sonic2000gr/RainbowProject/Schematics/IO Decoder/rescue-backup/IODecoder-2018-12-28-10-11-45.sch

## KiCad design Schematics/IO Decoder/rescue-backup/IODecoder-2018-12-28-10-11-45.sch (2017-12-11)

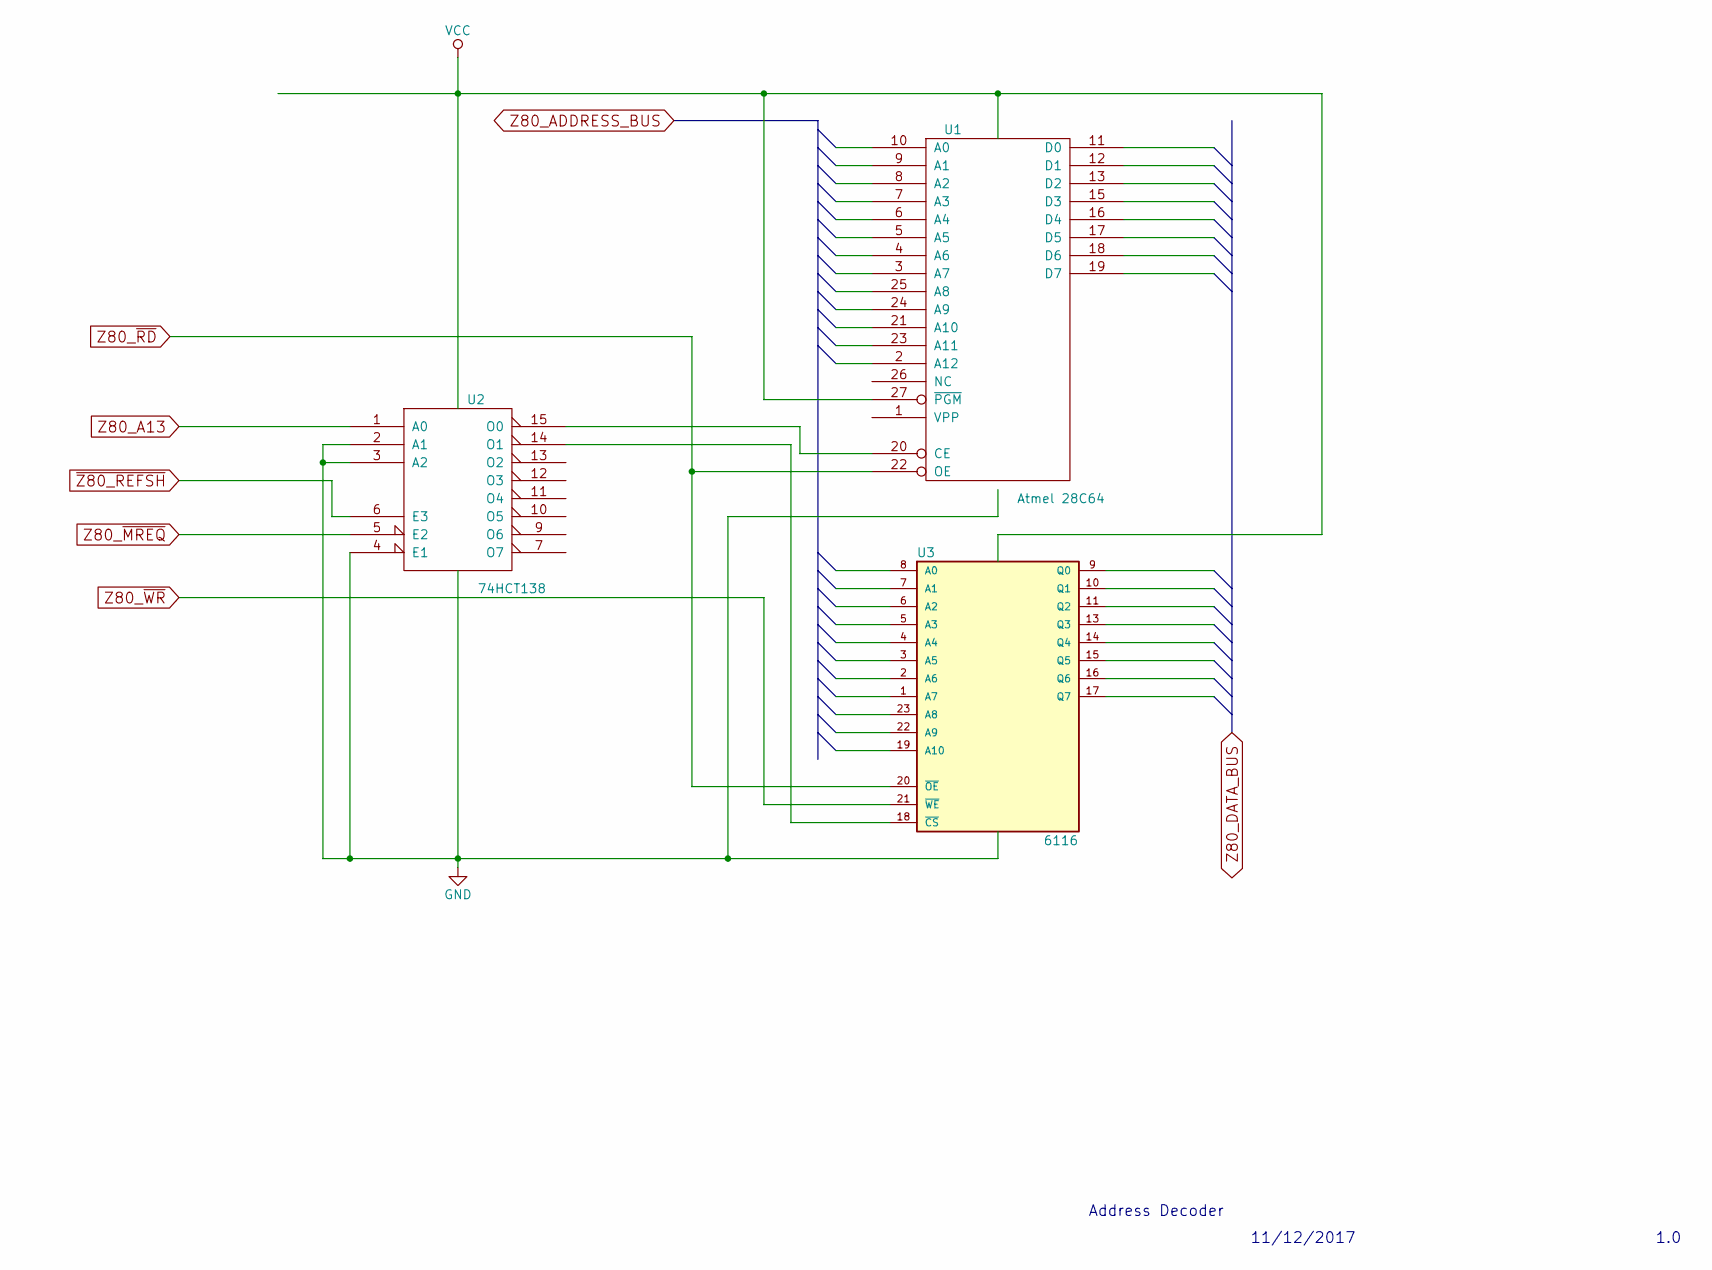
[picture p11: schematic IODecoder-2018-12-28-10-11-45.sch]

Parts:
U1: Atmel 28C64
U2: 74HCT138
U3: 6116

Connections:
GND: U1.14 (GND), U2.2 (A1), U2.3 (A2), U2.4 (E1), U2.8 (GND)
unnamed: U1.20 (CE), U2.15 (O0)
unnamed: U2.14 (O1), U3.18 (~CS)
VCC: U1.27 (~PGM), U2.16 (VCC)
Z80_A13: U2.1 (A0)
Z80_~MREQ: U2.5 (E2)
Z80_~RD: U1.22 (OE), U3.20 (~OE)
Z80_~WR: U3.21 (~WE)
~Z80_REFSH: U2.6 (E3)

Notes on the sheet:
Address Decoder
11/12/2017
1.0
